no010/ESProbe/fw/components/DAP/source/spi_switch.c

/**
 * @file spi_switch.c
 * @author windowsair
 * @brief Switching between SPI mode and IO mode
 * @change: 2020-11-25 first version
 *          2021-2-11 Transmission mode switching test passed
 *          2022-9-15 Support ESP32C3
 * @version 0.4
 * @date 2021-9-15
 *
 * @copyright MIT License
 *
 */
#include "sdkconfig.h"

#include <stdbool.h>

#include "components/DAP/include/cmsis_compiler.h"
#include "components/DAP/include/spi_switch.h"
#include "components/DAP/include/gpio_common.h"

#ifdef CONFIG_IDF_TARGET_ESP32C3
#include "hal/cpu_ll.h"
#endif

#ifdef CONFIG_IDF_TARGET_ESP8266
    #define DAP_SPI SPI1
#elif defined CONFIG_IDF_TARGET_ESP32
    #define DAP_SPI SPI2
    // Note that the index starts at 0, so we are using function 2(SPI).
    #define FUNC_SPI 1
    #define SPI2_HOST 1
    #define SPI_LL_RST_MASK (SPI_OUT_RST | SPI_IN_RST | SPI_AHBM_RST | SPI_AHBM_FIFO_RST)
#elif defined CONFIG_IDF_TARGET_ESP32C3
    #define DAP_SPI GPSPI2
#elif defined CONFIG_IDF_TARGET_ESP32S3
    #define DAP_SPI GPSPI2
#else
    #error unknown hardware
#endif



#define ENTER_CRITICAL() portENTER_CRITICAL()
#define EXIT_CRITICAL() portEXIT_CRITICAL()

typedef enum {
    SPI_40MHz_DIV = 2,
    // SPI_80MHz_DIV = 1, //// FIXME: high speed clock
} spi_clk_div_t;



#ifdef CONFIG_IDF_TARGET_ESP8266
/**
 * @brief Initialize on first use
 *
 */
void DAP_SPI_Init()
{
    // The driving of GPIO should be stopped,
    // otherwise SPI has potential timing issues (This issue has been identified in OpenOCD)
    GPIO.out_w1tc = (0x1 << 13);
    GPIO.out_w1tc = (0x1 << 14);

    // Disable flash operation mode
    DAP_SPI.user.flash_mode = false;

    // Set to Master mode
    DAP_SPI.pin.slave_mode = false;
    DAP_SPI.slave.slave_mode = false;

    // Master uses the entire hardware buffer to improve transmission speed
    // If the following fields are enabled, only a part of the buffer is used
    DAP_SPI.user.usr_mosi_highpart = false;
    DAP_SPI.user.usr_miso_highpart = false;

    // Disable cs pin
    DAP_SPI.user.cs_setup = false;
    DAP_SPI.user.cs_hold = false;

    // Duplex transmit
    DAP_SPI.user.duplex = true;

    // SCLK delay setting
    DAP_SPI.user.ck_i_edge = true;
    DAP_SPI.ctrl2.mosi_delay_num = 0;
    DAP_SPI.ctrl2.miso_delay_num = 0;

    // DIO & QIO SPI disable
    DAP_SPI.user.fwrite_dual = false;
    DAP_SPI.user.fwrite_quad = false;
    DAP_SPI.user.fwrite_dio  = false;
    DAP_SPI.user.fwrite_qio  = false;
    DAP_SPI.ctrl.fread_dual  = false;
    DAP_SPI.ctrl.fread_quad  = false;
    DAP_SPI.ctrl.fread_dio   = false;
    DAP_SPI.ctrl.fread_qio   = false;
    DAP_SPI.ctrl.fastrd_mode = true;

    // Enable soft reset
    DAP_SPI.slave.sync_reset = true;

    // Set the clock polarity and phase CPOL = 1, CPHA = 0
    DAP_SPI.pin.ck_idle_edge = 1;  // HIGH while idle
    DAP_SPI.user.ck_out_edge = 0;


    // Set data bit order
    DAP_SPI.ctrl.wr_bit_order = 1; // SWD -> LSB
    DAP_SPI.ctrl.rd_bit_order = 1; // SWD -> LSB
    // Set data byte order
    DAP_SPI.user.wr_byte_order = 0;  // SWD -> litte_endian && Risc V -> litte_endian
    DAP_SPI.user.rd_byte_order = 0;  // SWD -> litte_endian && Risc V -> litte_endian

    // Set dummy
    DAP_SPI.user.usr_dummy = 0;

    // Initialize HSPI IO
    gpio_pin_reg_t pin_reg;

    PIN_FUNC_SELECT(PERIPHS_IO_MUX_MTMS_U, FUNC_HSPI_CLK); // GPIO14 is SPI CLK pin (Clock)
    GPIO.enable_w1ts |= (0x1 << 14); // PP Output
    pin_reg.val = READ_PERI_REG(GPIO_PIN_REG(14));
    pin_reg.pullup = 1;
    WRITE_PERI_REG(GPIO_PIN_REG(14), pin_reg.val);

    PIN_FUNC_SELECT(PERIPHS_IO_MUX_MTCK_U, FUNC_HSPID_MOSI); // GPIO13 is SPI MOSI pin (Master Data Out)
    GPIO.enable_w1ts |= (0x1 << 13);
    GPIO.pin[13].driver = 0; // PP Output or OD output
    pin_reg.val = READ_PERI_REG(GPIO_PIN_REG(13));
    pin_reg.pullup = 0;
    WRITE_PERI_REG(GPIO_PIN_REG(13), pin_reg.val);

#if (USE_SPI_SIO != 1)
    PIN_FUNC_SELECT(PERIPHS_IO_MUX_MTDI_U, FUNC_HSPIQ_MISO); // GPIO12 is SPI MISO pin (Master Data In)
    // esp8266 in is always connected
    pin_reg.val = READ_PERI_REG(GPIO_PIN_REG(12));
    pin_reg.pullup = 0;
    WRITE_PERI_REG(GPIO_PIN_REG(12), pin_reg.val);
#endif // (USE_SPI_SIO != 1)



    // Set spi clk div
    CLEAR_PERI_REG_MASK(PERIPHS_IO_MUX_CONF_U, SPI1_CLK_EQU_SYS_CLK);

    DAP_SPI.clock.clk_equ_sysclk = false;
    DAP_SPI.clock.clkdiv_pre = 0;
    DAP_SPI.clock.clkcnt_n = SPI_40MHz_DIV - 1;
    DAP_SPI.clock.clkcnt_h = SPI_40MHz_DIV / 2 - 1;
    DAP_SPI.clock.clkcnt_l = SPI_40MHz_DIV - 1;

    // Do not use command and addr
    DAP_SPI.user.usr_command = 0;
    DAP_SPI.user.usr_addr = 0;
}
#elif defined CONFIG_IDF_TARGET_ESP32
void DAP_SPI_Init()
{
    // In esp32, the driving of GPIO should be stopped,
    // otherwise there will be issue in the spi
    GPIO.out_w1tc = (0x1 << 13);
    GPIO.out_w1tc = (0x1 << 14);

    // Enable spi module, We use SPI2(HSPI)
    DPORT_SET_PERI_REG_MASK(DPORT_PERIP_CLK_EN_REG, DPORT_SPI2_CLK_EN);
    DPORT_CLEAR_PERI_REG_MASK(DPORT_PERIP_RST_EN_REG, DPORT_SPI2_RST);


    // We will use IO_MUX to get the maximum speed.
    GPIO.func_in_sel_cfg[HSPID_IN_IDX].sig_in_sel = 0;   // IO_MUX direct connnect
    PIN_INPUT_ENABLE(IO_MUX_GPIO13_REG);                 // MOSI
    GPIO.func_out_sel_cfg[13].oen_sel = 0;               // use output enable signal from peripheral
    GPIO.func_out_sel_cfg[13].oen_inv_sel = 0;           // do not invert the output value
    PIN_FUNC_SELECT(IO_MUX_GPIO13_REG, FUNC_SPI);

    // GPIO.func_in_sel_cfg[HSPIQ_IN_IDX].sig_in_sel = 0;
    // PIN_INPUT_ENABLE(IO_MUX_GPIO12_REG);                 // MISO
    // GPIO.func_out_sel_cfg[12].oen_sel = 0;
    // GPIO.func_out_sel_cfg[12].oen_inv_sel = 0;
    // PIN_FUNC_SELECT(IO_MUX_GPIO12_REG, FUNC_SPI);

    GPIO.func_in_sel_cfg[HSPICLK_IN_IDX].sig_in_sel = 0;
    PIN_INPUT_ENABLE(IO_MUX_GPIO14_REG);                 // SCLK
    GPIO.func_out_sel_cfg[14].oen_sel = 0;
    GPIO.func_out_sel_cfg[14].oen_inv_sel = 0;
    PIN_FUNC_SELECT(IO_MUX_GPIO14_REG, FUNC_SPI);


    // Not using DMA
    // esp32 only
    DPORT_SET_PERI_REG_BITS(DPORT_SPI_DMA_CHAN_SEL_REG, 3, 0, (SPI2_HOST * 2));


    // Reset DMA
    DAP_SPI.dma_conf.val |= SPI_LL_RST_MASK;
    DAP_SPI.dma_out_link.start = 0;
    DAP_SPI.dma_in_link.start = 0;
    DAP_SPI.dma_conf.val &= ~SPI_LL_RST_MASK;
    // Disable DMA
    DAP_SPI.dma_conf.dma_continue = 0;


    // Set to Master mode
    DAP_SPI.slave.slave_mode = false;


    // use all 64 bytes of the buffer
    DAP_SPI.user.usr_mosi_highpart = false;
    DAP_SPI.user.usr_miso_highpart = false;


    // Disable cs pin
    DAP_SPI.user.cs_setup = false;
    DAP_SPI.user.cs_hold = false;

    // Disable CS signal
    DAP_SPI.pin.cs0_dis = 1;
    DAP_SPI.pin.cs1_dis = 1;
    DAP_SPI.pin.cs2_dis = 1;

    // Duplex transmit
    DAP_SPI.user.doutdin = false;  // half dulex


    // Set data bit order
    DAP_SPI.ctrl.wr_bit_order = 1;   // SWD -> LSB
    DAP_SPI.ctrl.rd_bit_order = 1;   // SWD -> LSB
    // Set data byte order
    DAP_SPI.user.wr_byte_order = 0;  // SWD -> litte_endian && Risc V -> litte_endian
    DAP_SPI.user.rd_byte_order = 0;  // SWD -> litte_endian && Risc V -> litte_endian

    // Set dummy
    DAP_SPI.user.usr_dummy = 0; // not use

    // Set spi clk: 40Mhz 50% duty
    // CLEAR_PERI_REG_MASK(PERIPHS_IO_MUX_CONF_U, SPI1_CLK_EQU_SYS_CLK);

    // See esp32 TRM `SPI_CLOCK_REG`
    DAP_SPI.clock.clk_equ_sysclk = false;
    DAP_SPI.clock.clkdiv_pre = 0;
    DAP_SPI.clock.clkcnt_n = SPI_40MHz_DIV - 1;
    DAP_SPI.clock.clkcnt_h = SPI_40MHz_DIV / 2 - 1;
    DAP_SPI.clock.clkcnt_l = SPI_40MHz_DIV - 1;
    // Dummy is not required, but it may still need to be delayed
    // by half a clock cycle (espressif)


    // MISO delay setting
    DAP_SPI.user.ck_i_edge = true; //// TODO: may be used in slave mode?
    DAP_SPI.ctrl2.miso_delay_mode = 0;
    DAP_SPI.ctrl2.miso_delay_num = 0;


    // Set the clock polarity and phase CPOL = 1, CPHA = 0
    DAP_SPI.pin.ck_idle_edge = 1;  // HIGH while idle
    DAP_SPI.user.ck_out_edge = 0;

    // No command and addr for now
    DAP_SPI.user.usr_command = 0;
    DAP_SPI.user.usr_addr = 0;
}
#elif defined CONFIG_IDF_TARGET_ESP32C3
void DAP_SPI_Init()
{
    periph_ll_enable_clk_clear_rst(PERIPH_SPI2_MODULE);

    // In esp32, the driving of GPIO should be stopped,
    // otherwise there will be issue in the spi
    gpio_ll_set_level(&GPIO, GPIO_NUM_6, 0);
    gpio_ll_set_level(&GPIO, GPIO_NUM_7, 0);


    // We will use IO_MUX to get the maximum speed.
    GPIO.func_in_sel_cfg[FSPID_IN_IDX].sig_in_sel = 0;   // IO_MUX direct connnect
    PIN_INPUT_ENABLE(IO_MUX_GPIO7_REG);                  // MOSI
    GPIO.func_out_sel_cfg[7].oen_sel = 0;               // use output enable signal from peripheral
    GPIO.func_out_sel_cfg[7].oen_inv_sel = 0;           // do not invert the output value
    PIN_FUNC_SELECT(IO_MUX_GPIO7_REG, FUNC_MTDO_FSPID);


    GPIO.func_in_sel_cfg[FSPICLK_IN_IDX].sig_in_sel = 0;
    PIN_INPUT_ENABLE(IO_MUX_GPIO6_REG);                 // SCLK
    GPIO.func_out_sel_cfg[6].oen_sel = 0;
    GPIO.func_out_sel_cfg[6].oen_inv_sel = 0;
    PIN_FUNC_SELECT(IO_MUX_GPIO6_REG, FUNC_MTCK_FSPICLK);


    // Not using DMA
    // esp32c3 only
    DAP_SPI.user.usr_conf_nxt = 0;
    DAP_SPI.slave.usr_conf = 0;
    DAP_SPI.dma_conf.dma_rx_ena = 0;
    DAP_SPI.dma_conf.dma_tx_ena = 0;

    // Set to Master mode
    DAP_SPI.slave.slave_mode = false;

    // use all 64 bytes of the buffer
    DAP_SPI.user.usr_mosi_highpart = false;
    DAP_SPI.user.usr_miso_highpart = false;

    // Disable cs pin
    DAP_SPI.user.cs_setup = false;
    DAP_SPI.user.cs_hold = false;

    // Disable CS signal
    DAP_SPI.misc.cs0_dis = 1;
    DAP_SPI.misc.cs1_dis = 1;
    DAP_SPI.misc.cs2_dis = 1;
    DAP_SPI.misc.cs3_dis = 1;
    DAP_SPI.misc.cs4_dis = 1;
    DAP_SPI.misc.cs5_dis = 1;

    // Duplex transmit
    DAP_SPI.user.doutdin = false;  // half dulex

    // Set data bit order
    DAP_SPI.ctrl.wr_bit_order = 1;   // SWD -> LSB
    DAP_SPI.ctrl.rd_bit_order = 1;   // SWD -> LSB

    // Set dummy
    DAP_SPI.user.usr_dummy = 0; // not use

    // Set spi clk: 40Mhz 50% duty
    // CLEAR_PERI_REG_MASK(PERIPHS_IO_MUX_CONF_U, SPI1_CLK_EQU_SYS_CLK);

    // See esp32c3 TRM `SPI_CLOCK_REG`
    DAP_SPI.clock.clk_equ_sysclk = false;
    DAP_SPI.clock.clkdiv_pre = 0;
    DAP_SPI.clock.clkcnt_n = SPI_40MHz_DIV - 1;
    DAP_SPI.clock.clkcnt_h = SPI_40MHz_DIV / 2 - 1;
    DAP_SPI.clock.clkcnt_l = SPI_40MHz_DIV - 1;

    // MISO delay setting
    DAP_SPI.user.rsck_i_edge = true;
    DAP_SPI.din_mode.din0_mode = 0;
    DAP_SPI.din_mode.din1_mode = 0;
    DAP_SPI.din_mode.din2_mode = 0;
    DAP_SPI.din_mode.din3_mode = 0;
    DAP_SPI.din_num.din0_num = 0;
    DAP_SPI.din_num.din1_num = 0;
    DAP_SPI.din_num.din2_num = 0;
    DAP_SPI.din_num.din3_num = 0;

    // Set the clock polarity and phase CPOL = 1, CPHA = 0
    DAP_SPI.misc.ck_idle_edge = 1;  // HIGH while idle
    DAP_SPI.user.ck_out_edge = 0;

    // enable spi clock
    DAP_SPI.clk_gate.clk_en = 1;
    DAP_SPI.clk_gate.mst_clk_active = 1;
    DAP_SPI.clk_gate.mst_clk_sel = 1;

    // No command and addr for now
    DAP_SPI.user.usr_command = 0;
    DAP_SPI.user.usr_addr = 0;
}
#elif defined CONFIG_IDF_TARGET_ESP32S3
void DAP_SPI_Init()
{
    periph_ll_enable_clk_clear_rst(PERIPH_SPI2_MODULE);

    // In esp32, the driving of GPIO should be stopped,
    // otherwise there will be issue in the spi
    gpio_ll_set_level(&GPIO, GPIO_NUM_12, 0);
    gpio_ll_set_level(&GPIO, GPIO_NUM_11, 0);

    // We will use IO_MUX to get the maximum speed.
    gpio_ll_iomux_in(&GPIO, GPIO_NUM_12,FSPICLK_IN_IDX);
    gpio_ll_iomux_out(&GPIO, GPIO_NUM_12, FUNC_GPIO12_FSPICLK, 0);

    gpio_ll_iomux_in(&GPIO, GPIO_NUM_11,FSPID_IN_IDX);
    gpio_ll_iomux_out(&GPIO, GPIO_NUM_11, FUNC_GPIO11_FSPID, 0);

    GPIO.func_out_sel_cfg[GPIO_NUM_11].oen_sel = 0;
    GPIO.func_out_sel_cfg[GPIO_NUM_12].oen_sel = 0;

    // Not using DMA
    DAP_SPI.user.usr_conf_nxt = 0;
    DAP_SPI.slave.usr_conf = 0;
    DAP_SPI.dma_conf.dma_rx_ena = 0;
    DAP_SPI.dma_conf.dma_tx_ena = 0;

    // Set to Master mode
    DAP_SPI.slave.slave_mode = false;

    // use all 64 bytes of the buffer
    DAP_SPI.user.usr_mosi_highpart = false;
    DAP_SPI.user.usr_miso_highpart = false;

    // Disable cs pin
    DAP_SPI.user.cs_setup = false;
    DAP_SPI.user.cs_hold = false;

    // Disable CS signal
    DAP_SPI.misc.cs0_dis = 1;
    DAP_SPI.misc.cs1_dis = 1;
    DAP_SPI.misc.cs2_dis = 1;
    DAP_SPI.misc.cs3_dis = 1;
    DAP_SPI.misc.cs4_dis = 1;
    DAP_SPI.misc.cs5_dis = 1;

    // Duplex transmit
    DAP_SPI.user.doutdin = false;  // half dulex

    // Set data bit order
    DAP_SPI.ctrl.wr_bit_order = 1;   // SWD -> LSB
    DAP_SPI.ctrl.rd_bit_order = 1;   // SWD -> LSB

    // Set dummy
    DAP_SPI.user.usr_dummy = 0; // not use

    // Set spi clk: 40Mhz 50% duty
    // CLEAR_PERI_REG_MASK(PERIPHS_IO_MUX_CONF_U, SPI1_CLK_EQU_SYS_CLK);

    // See TRM `SPI_CLOCK_REG`
    DAP_SPI.clock.clk_equ_sysclk = false;
    DAP_SPI.clock.clkdiv_pre = 0;
    DAP_SPI.clock.clkcnt_n = SPI_40MHz_DIV - 1;
    DAP_SPI.clock.clkcnt_h = SPI_40MHz_DIV / 2 - 1;
    DAP_SPI.clock.clkcnt_l = SPI_40MHz_DIV - 1;

    // MISO delay setting
    DAP_SPI.user.rsck_i_edge = true;
    DAP_SPI.din_mode.din0_mode = 0;
    DAP_SPI.din_mode.din1_mode = 0;
    DAP_SPI.din_mode.din2_mode = 0;
    DAP_SPI.din_mode.din3_mode = 0;
    DAP_SPI.din_num.din0_num = 0;
    DAP_SPI.din_num.din1_num = 0;
    DAP_SPI.din_num.din2_num = 0;
    DAP_SPI.din_num.din3_num = 0;

    // Set the clock polarity and phase CPOL = 1, CPHA = 0
    DAP_SPI.misc.ck_idle_edge = 1;  // HIGH while idle
    DAP_SPI.user.ck_out_edge = 0;

    // enable spi clock
    DAP_SPI.clk_gate.clk_en = 1;
    DAP_SPI.clk_gate.mst_clk_active = 1;
    DAP_SPI.clk_gate.mst_clk_sel = 1;

    // No command and addr for now
    DAP_SPI.user.usr_command = 0;
    DAP_SPI.user.usr_addr = 0;
}
#endif


#ifdef CONFIG_IDF_TARGET_ESP8266
/**
 * @brief Switch to GPIO
 * Note: You may be able to pull the pin high in SPI mode, though you cannot set it to LOW
 */
__FORCEINLINE void DAP_SPI_Deinit()
{
    PIN_FUNC_SELECT(PERIPHS_IO_MUX_MTMS_U, FUNC_GPIO14);
    PIN_FUNC_SELECT(PERIPHS_IO_MUX_MTCK_U, FUNC_GPIO13); // MOSI
    // enable SWCLK output
    GPIO.enable_w1ts = 0x01 << 14;

    // enable MOSI output & input
    GPIO.enable_w1ts = 0x1 << 13;
}
#elif defined CONFIG_IDF_TARGET_ESP32
__FORCEINLINE void DAP_SPI_Deinit()
{
    PIN_FUNC_SELECT(GPIO_PIN_MUX_REG[14], PIN_FUNC_GPIO);
    PIN_FUNC_SELECT(GPIO_PIN_MUX_REG[13], PIN_FUNC_GPIO); // MOSI

    // enable SWCLK output
    GPIO.enable_w1ts = 0x01 << 14;

    // enable MOSI output & input
    GPIO.enable_w1ts = 0x1 << 13;
    PIN_INPUT_ENABLE(GPIO_PIN_MUX_REG[13]);
}
#elif defined CONFIG_IDF_TARGET_ESP32C3
__FORCEINLINE void DAP_SPI_Deinit()
{
    PIN_FUNC_SELECT(GPIO_PIN_MUX_REG[6], PIN_FUNC_GPIO);
    PIN_FUNC_SELECT(GPIO_PIN_MUX_REG[7], PIN_FUNC_GPIO); // MOSI

    // Route GPIO output to software-controlled GPIO_OUT_REG (SIG_GPIO_OUT_IDX=256)
    // instead of dedic_gpio (CPU_GPIO_OUTx_IDX), since dedic_gpio CSR instructions
    // are not available in ESP-IDF 5.5 and gpio_ll_set_level() writes GPIO_OUT_REG.
    GPIO.func_out_sel_cfg[GPIO_NUM_6].out_sel = SIG_GPIO_OUT_IDX;
    GPIO.func_out_sel_cfg[GPIO_NUM_6].oen_sel = 0;

    GPIO.func_out_sel_cfg[GPIO_NUM_7].out_sel = SIG_GPIO_OUT_IDX;
    GPIO.func_out_sel_cfg[GPIO_NUM_7].oen_sel = 0;

    GPIO.func_in_sel_cfg[FSPID_IN_IDX].sig_in_sel = 0;
    GPIO.func_in_sel_cfg[FSPID_IN_IDX].in_sel = GPIO_NUM_7;

    // enable SWCLK/MOSI output
    gpio_ll_output_enable(&GPIO, GPIO_NUM_6);
    gpio_ll_output_enable(&GPIO, GPIO_NUM_7);
    PIN_INPUT_ENABLE(GPIO_PIN_MUX_REG[7]);
}
#elif defined CONFIG_IDF_TARGET_ESP32S3
__FORCEINLINE void DAP_SPI_Deinit()
{
    gpio_ll_iomux_func_sel(GPIO_PIN_MUX_REG[GPIO_NUM_12], PIN_FUNC_GPIO);
    gpio_ll_iomux_func_sel(GPIO_PIN_MUX_REG[GPIO_NUM_11], PIN_FUNC_GPIO); // MOSI

    // SWCLK output
    GPIO.func_out_sel_cfg[GPIO_NUM_12].func_sel = CORE1_GPIO_OUT1_IDX;
    GPIO.func_out_sel_cfg[GPIO_NUM_12].oen_sel = 1;
    gpio_ll_output_enable(&GPIO, GPIO_NUM_12);

    // SWDIO outout
    GPIO.func_out_sel_cfg[GPIO_NUM_11].func_sel = CORE1_GPIO_OUT0_IDX;
    GPIO.func_out_sel_cfg[GPIO_NUM_11].oen_sel = 1;
    gpio_ll_output_enable(&GPIO, GPIO_NUM_11);

    // SWDIO input
    GPIO.func_in_sel_cfg[CORE1_GPIO_IN0_IDX].sig_in_sel = 1;
    GPIO.func_in_sel_cfg[CORE1_GPIO_IN0_IDX].func_sel = GPIO_NUM_11;
    gpio_ll_input_enable(&GPIO, GPIO_NUM_11);
}
#endif


#ifdef CONFIG_IDF_TARGET_ESP32
/**
 * @brief Gain control of SPI
 *
 */
__FORCEINLINE void DAP_SPI_Acquire()
{
    PIN_FUNC_SELECT(IO_MUX_GPIO14_REG, FUNC_SPI);
}


/**
 * @brief Release control of SPI
 *
 */
__FORCEINLINE void DAP_SPI_Release()
{
    PIN_FUNC_SELECT(GPIO_PIN_MUX_REG[14], PIN_FUNC_GPIO);
    GPIO.enable_w1ts = (0x01 << 14);
}
#elif defined CONFIG_IDF_TARGET_ESP32C3
__FORCEINLINE void DAP_SPI_Acquire()
{
    PIN_FUNC_SELECT(IO_MUX_GPIO6_REG, FUNC_MTCK_FSPICLK);
}

__FORCEINLINE void DAP_SPI_Release()
{
    PIN_FUNC_SELECT(IO_MUX_GPIO6_REG, FUNC_MTCK_GPIO6);
}
#elif defined CONFIG_IDF_TARGET_ESP32S3
/**
 * @brief Gain control of SPI
 *
 */
__FORCEINLINE void DAP_SPI_Acquire()
{
    gpio_ll_iomux_func_sel(GPIO_PIN_MUX_REG[GPIO_NUM_12], FUNC_GPIO12_FSPICLK);
}


/**
 * @brief Release control of SPI
 *
 */
__FORCEINLINE void DAP_SPI_Release()
{
    gpio_ll_iomux_func_sel(GPIO_PIN_MUX_REG[GPIO_NUM_12], FUNC_GPIO12_GPIO12);
}
#endif
