no010/ESProbe/fw/main/usbip_server.c

#include <stdint.h>
#include <string.h>

#include "main/usbip_server.h"
#include "main/DAP_handle.h"
#include "main/wifi_configuration.h"

#include "components/USBIP/usb_handle.h"
#include "components/USBIP/usb_descriptor.h"

#include "lwip/err.h"
#include "lwip/sockets.h"
#include "lwip/sys.h"
#include <lwip/netdb.h>

#ifndef likely
#define likely(x)      __builtin_expect(!!(x), 1)
#endif

#ifndef unlikely
#define unlikely(x)    __builtin_expect(!!(x), 0)
#endif

// Set to 1 to enable verbose hex-dump logging (slows down USB enumeration)
#define USBIP_DEBUG_VERBOSE 0

// attach helper function
static int read_stage1_command(uint8_t *buffer, uint32_t length);
static void handle_device_list(uint8_t *buffer, uint32_t length);
static void handle_device_attach(uint8_t *buffer, uint32_t length);
static void send_stage1_header(uint16_t command, uint32_t status);
static void send_device_list();
static void send_device_info();
static void send_interface_info();

// emulate helper function
static void pack(void *data, int size);
static void unpack(void *data, int size);

static void handle_unlink(usbip_stage2_header *header);
// unlink helper function
static void send_stage2_unlink(usbip_stage2_header *req_header);


#if (USBIP_DEBUG_VERBOSE == 1)
static void debug_dump_bytes(const char *tag, const uint8_t *data, size_t length)
{
    char line[128];
    size_t offset = 0;

    while (offset < length) {
        size_t chunk = ((length - offset) > 16U) ? 16U : (length - offset);
        int pos = snprintf(line, sizeof(line), "%s +%02u:", tag, (unsigned)offset);
        for (size_t i = 0; i < chunk && pos > 0 && pos < (int)sizeof(line); ++i) {
            pos += snprintf(&line[pos], sizeof(line) - (size_t)pos, " %02X", data[offset + i]);
        }
        os_printf("%s\r\n", line);
        offset += chunk;
    }
}

static void debug_dump_usbip_header(const char *tag, const usbip_stage2_header *header)
{
    debug_dump_bytes(tag, (const uint8_t *)header, sizeof(usbip_stage2_header));
}
#else
#define debug_dump_bytes(tag, data, length)     ((void)0)
#define debug_dump_usbip_header(tag, header)    ((void)0)
#endif

int usbip_network_send(int s, const void *dataptr, size_t size, int flags) {
#if (USE_KCP == 1)
    return kcp_network_send(dataptr, size);
#elif (USE_TCP_NETCONN == 1)
    return tcp_netconn_send(dataptr, size);
#else // BSD style
    const uint8_t *data = (const uint8_t *)dataptr;
    size_t remaining = size;

    while (remaining > 0) {
        int sent = send(s, data, remaining, flags);
        if (sent <= 0) {
            return sent;
        }
        data += sent;
        remaining -= (size_t)sent;
    }

    return (int)size;
#endif
}

static int attach(uint8_t *buffer, uint32_t length)
{
    int command = read_stage1_command(buffer, length);
    if (command < 0)
    {
        return -1;
    }

    switch (command)
    {
    case USBIP_STAGE1_CMD_DEVICE_LIST: // OP_REQ_DEVLIST
        handle_device_list(buffer, length);
        break;

    case USBIP_STAGE1_CMD_DEVICE_ATTACH: // OP_REQ_IMPORT
        handle_device_attach(buffer, length);
        break;

    default:
        os_printf("attach Unknown command: %d\r\n", command);
        break;
    }
    return 0;
}

static int read_stage1_command(uint8_t *buffer, uint32_t length)
{
    if (length < sizeof(usbip_stage1_header))
    {
        return -1;
    }
    usbip_stage1_header *req = (usbip_stage1_header *)buffer;
    uint16_t cmd_raw = req->command;
    int cmd = (int)(ntohs(req->command) & 0xFF);
    os_printf("read_stage1_command: raw=0x%04X ret=0x%02X buf=%02X%02X%02X%02X%02X%02X%02X%02X\r\n",
              (unsigned)cmd_raw, (unsigned)cmd,
              buffer[0], buffer[1], buffer[2], buffer[3],
              buffer[4], buffer[5], buffer[6], buffer[7]);
    return cmd;
}

static void handle_device_list(uint8_t *buffer, uint32_t length)
{
    os_printf("Handling dev list request...\r\n");
    send_stage1_header(USBIP_STAGE1_CMD_DEVICE_LIST, 0);
    send_device_list();
}

static void handle_device_attach(uint8_t *buffer, uint32_t length)
{
    os_printf("Handling dev attach request...\r\n");

    //char bus[USBIP_BUSID_SIZE];
    if (length < sizeof(USBIP_BUSID_SIZE))
    {
        os_printf("handle device attach failed!\r\n");
        return;
    }
    //client.readBytes((uint8_t *)bus, USBIP_BUSID_SIZE);

    send_stage1_header(USBIP_STAGE1_CMD_DEVICE_ATTACH, 0);

    send_device_info();
}

static void send_stage1_header(uint16_t command, uint32_t status)
{
    os_printf("Sending header...\r\n");
    usbip_stage1_header header = {0};
    header.version = htons(273); ////TODO:  273???
    // may be : https://github.com/Oxalin/usbip_windows/issues/4

    header.command = htons(command);
    header.status = htonl(status);

    usbip_network_send(kSock, (uint8_t *)&header, sizeof(usbip_stage1_header), 0);
}

static void send_device_list()
{
    os_printf("Sending device list...\r\n");

    // send device list size:
    os_printf("Sending device list size...\r\n");
    usbip_stage1_response_devlist response_devlist = {0};

    // we have only 1 device, so:
    response_devlist.list_size = htonl(1);

    usbip_network_send(kSock, (uint8_t *)&response_devlist, sizeof(usbip_stage1_response_devlist), 0);

    // may be foreach:

    {
        // send device info:
        send_device_info();
        // send device interfaces: // (1)
        send_interface_info();
    }
}

static void send_device_info()
{
    os_printf("Sending device info...\r\n");
    usbip_stage1_usb_device device = {0};

    strcpy(device.path, "/sys/devices/pci0000:00/0000:00:01.2/usb1/1-1");
    strcpy(device.busid, "1-1");

    device.busnum = htonl(1);
    device.devnum = htonl(1);
    device.speed = htonl(2); // USB_SPEED_FULL (12 Mbps).  WiFi cannot sustain High Speed.

    device.idVendor = htons(USBD0_DEV_DESC_IDVENDOR);
    device.idProduct = htons(USBD0_DEV_DESC_IDPRODUCT);
    device.bcdDevice = htons(USBD0_DEV_DESC_BCDDEVICE);

    device.bDeviceClass = 0x00; // We need to use a device other than the USB-IF standard, set to 0x00
    device.bDeviceSubClass = 0x00;
    device.bDeviceProtocol = 0x00;

    device.bConfigurationValue = 1;
    device.bNumConfigurations = 1;
    device.bNumInterfaces = 1;

    usbip_network_send(kSock, (uint8_t *)&device, sizeof(usbip_stage1_usb_device), 0);
}

static void send_interface_info()
{
    os_printf("Sending interface info...\r\n");
    usbip_stage1_usb_interface interface = {0};
    interface.bInterfaceClass = USBD_CUSTOM_CLASS0_IF0_CLASS;
    interface.bInterfaceSubClass = USBD_CUSTOM_CLASS0_IF0_SUBCLASS;
    interface.bInterfaceProtocol = USBD_CUSTOM_CLASS0_IF0_PROTOCOL;
    interface.padding = 0; // shall be set to zero

    usbip_network_send(kSock, (uint8_t *)&interface, sizeof(usbip_stage1_usb_interface), 0);
}

static int usbip_urb_process(uint8_t *base, uint32_t length)
{
    usbip_stage2_header *header = (usbip_stage2_header *)base;
    uint8_t *data;
    uint32_t command, dir, ep;
    uint32_t unlink_count = 0;
    bool may_has_data;
    int sz, ret;
    int dap_req_num = 0;
    uint32_t ep_data_length = 0;

    while (1) {
        // header
        data = base;
        sz = 48; // for USBIP_CMD_SUBMIT/USBIP_CMD_UNLINK
        do {
            ret = recv(kSock, data, sz, 0);
            if (ret <= 0)
                goto out;
            sz -= ret;
            data += ret;
        } while (sz > 0);

        command = ntohl(header->base.command);
        dir = ntohl(header->base.direction);
        ep = ntohl(header->base.ep);
        may_has_data = (command == USBIP_STAGE2_REQ_SUBMIT && dir == USBIP_DIR_OUT);
        ep_data_length = may_has_data ? ntohl(header->u.cmd_submit.data_length) : 0;
        sz = (int)ep_data_length;

        while (sz) {
                ret = recv(kSock, data, sz, 0);
                if (ret <= 0)
                    goto out;
                sz -= ret;
                data += ret;
        }

        if (likely(command == USBIP_STAGE2_REQ_SUBMIT)) {
            if (likely(ep == 1 && dir == USBIP_DIR_IN)) {
                if (dap_req_num > 0) {
                    int fr = fast_reply(base, sizeof(usbip_stage2_header), dap_req_num);
                    if (fr) {
                        dap_req_num--;
                    } else {
                        save_in_header(header);
                    }
                } else {
                    // No OUT pending yet (flush read from start_rx() or race).
                    // Return an empty ACK immediately so the host does not
                    // timeout and UNLINK.  With the pyusb_v2_backend patch
                    // OUT now arrives before IN for real commands.
                    fast_reply(base, sizeof(usbip_stage2_header), 0);
                }
            } else if (likely(ep == 1 && dir == USBIP_DIR_OUT)) {
                dap_req_num++;
                handle_dap_data_request(header, ep_data_length);
            } else if (ep == 0) {
                unpack(base, sizeof(usbip_stage2_header));
#if (USBIP_DEBUG_VERBOSE == 1)
                os_printf("EP0_REQ seq=%lu dir=%lu ep=%lu len=%ld type=%02X req=%02X wValue=%02X%02X wIndex=%02X%02X wLength=%02X%02X\r\n",
                          (unsigned long)header->base.seqnum,
                          (unsigned long)header->base.direction,
                          (unsigned long)header->base.ep,
                          (long)header->u.cmd_submit.data_length,
                          header->u.cmd_submit.request.bmRequestType,
                          header->u.cmd_submit.request.bRequest,
                          header->u.cmd_submit.request.wValue.u8hi,
                          header->u.cmd_submit.request.wValue.u8lo,
                          header->u.cmd_submit.request.wIndex.u8hi,
                          header->u.cmd_submit.request.wIndex.u8lo,
                          header->u.cmd_submit.request.wLength.u8hi,
                          header->u.cmd_submit.request.wLength.u8lo);
                debug_dump_usbip_header("EP0_REQ_HDR", header);
#endif
                handleUSBControlRequest(header);
            } else {
                // ep3 reserved for SWO
                os_printf("ep reserved:%d\r\n", ep);
                send_stage2_submit(header, 0, 0);
            }
        } else if (command == USBIP_STAGE2_REQ_UNLINK) {
            if (unlink_count == 0 || unlink_count % 100 == 0)
                os_printf("unlink\r\n");
            unlink_count++;
            unpack(base, sizeof(usbip_stage2_header));
            handle_unlink(header);
        } else {
            os_printf("emulate unknown command:%d\r\n", command);
            return -1;
        }

        if (has_pending_in() && dap_req_num > 0) {
            usbip_stage2_header saved_header;
            if (peek_oldest_in_header(&saved_header)) {
                if (fast_reply((uint8_t *)&saved_header, sizeof(usbip_stage2_header), dap_req_num)) {
                    dap_req_num--;
                    get_oldest_in_header(&saved_header); // consume it
                }
            }
        }
    }

out:
    if (ret < 0)
        os_printf("recv failed: errno %d\r\n", errno);
    return ret;
}

int usbip_worker(uint8_t *base, uint32_t length, enum usbip_server_state_t *state)
{
    uint8_t *data;
    int pre_read_sz = 4;
    int sz, ret;

    os_printf("usbip_worker enter state=%d\r\n", (int)*state);

    // OP_REQ_DEVLIST status field
    if (*state == WAIT_DEVLIST) {
        data = base + 4;
        sz = 8 - pre_read_sz;
        do {
            ret = recv(kSock, data, sz, 0);
            if (ret <= 0)
                return ret;
            sz -= ret;
            data += ret;
        } while (sz > 0);

        os_printf("usbip_worker calling attach(base,8)\r\n");
        ret = attach(base, 8);
        if (ret)
            return ret;

        pre_read_sz = 0;
    }

    *state = WAIT_IMPORT;
    // OP_REQ_IMPORT
    data = base + pre_read_sz;
    sz = 40 - pre_read_sz;
    do {
        ret = recv(kSock, data, sz, 0);
        if (ret <= 0)
            return ret;
        sz -= ret;
        data += ret;
    } while (sz > 0);

    os_printf("usbip_worker calling attach(base,40)\r\n");
    ret = attach(base, 40);
    if (ret)
        return ret;

    // URB process
    *state = WAIT_URB;
    ret = usbip_urb_process(base, length);
    if (ret) {
        *state = WAIT_DEVLIST;
        return ret;
    }

    return 0;
}

/**
 * @brief Pack the following packets(Offset 0x00 - 0x28):
 *       - cmd_submit
 *       - ret_submit
 *       - cmd_unlink
 *       - ret_unlink
 *
 * @param data Point to packets header
 * @param size Packets header size
 */
static void pack(void *data, int size)
{

    // Ignore the setup field
    int sz = (size / sizeof(uint32_t)) - 2;
    uint32_t *ptr = (uint32_t *)data;

    for (int i = 0; i < sz; i++)
    {

        ptr[i] = htonl(ptr[i]);
    }
}

/**
 * @brief Unack the following packets(Offset 0x00 - 0x28):
 *       - cmd_submit
 *       - ret_submit
 *       - cmd_unlink
 *       - ret_unlink
 *
 * @param data Point to packets header
 * @param size  packets header size
 */
static void unpack(void *data, int size)
{

    // Ignore the setup field
    int sz = (size / sizeof(uint32_t)) - 2;
    uint32_t *ptr = (uint32_t *)data;

    for (int i = 0; i < sz; i++)
    {
        ptr[i] = ntohl(ptr[i]);
    }
}

void send_stage2_submit(usbip_stage2_header *req_header, int32_t status, int32_t data_length)
{
    uint32_t request_devid = req_header->base.devid;
    uint32_t request_direction = req_header->base.direction;
    uint32_t request_ep = req_header->base.ep;

    req_header->base.command = USBIP_STAGE2_RSP_SUBMIT;
    req_header->base.devid = request_devid;
    req_header->base.direction = !request_direction;
    req_header->base.ep = request_ep;

    memset(&(req_header->u), 0, sizeof(req_header->u));

    req_header->u.ret_submit.status = status;
    req_header->u.ret_submit.data_length = data_length;
    req_header->u.ret_submit.number_of_packets = 0;
    // already unpacked
    pack(req_header, sizeof(usbip_stage2_header));

#if (USBIP_DEBUG_VERBOSE == 1)
    if (ntohl(req_header->base.seqnum) != 0) {
        os_printf("RET_SUBMIT seq=%lu status=%ld len=%ld\r\n",
                  (unsigned long)ntohl(req_header->base.seqnum),
                  (long)status,
                  (long)data_length);
        debug_dump_usbip_header("RET_SUBMIT_HDR", req_header);
    }
#endif

    usbip_network_send(kSock, req_header, sizeof(usbip_stage2_header), 0);
}

void send_stage2_submit_data(usbip_stage2_header *req_header, int32_t status, const void *const data, int32_t data_length)
{
    uint8_t send_buf[sizeof(usbip_stage2_header) + 512];
    size_t total_len = sizeof(usbip_stage2_header);

    // Setup header (same logic as send_stage2_submit)
    uint32_t request_devid = req_header->base.devid;
    uint32_t request_direction = req_header->base.direction;
    uint32_t request_ep = req_header->base.ep;

    req_header->base.command = USBIP_STAGE2_RSP_SUBMIT;
    req_header->base.devid = request_devid;
    req_header->base.direction = !request_direction;
    req_header->base.ep = request_ep;

    memset(&(req_header->u), 0, sizeof(req_header->u));

    req_header->u.ret_submit.status = status;
    req_header->u.ret_submit.data_length = data_length;
    req_header->u.ret_submit.number_of_packets = 0;

    pack(req_header, sizeof(usbip_stage2_header));

    // Copy header + data into single buffer to avoid split-send latency
    memcpy(send_buf, req_header, sizeof(usbip_stage2_header));
    if (data && data_length > 0) {
        int32_t copy_len = data_length;
        if (copy_len > 512) {
            os_printf("WARN: send_stage2_submit_data len=%d > 512, truncating!\r\n", copy_len);
            copy_len = 512;
        }
        memcpy(send_buf + sizeof(usbip_stage2_header), data, copy_len);
        total_len += copy_len;
    }

    usbip_network_send(kSock, send_buf, total_len, 0);
}

void send_stage2_submit_data_fast(usbip_stage2_header *req_header, const void *const data, int32_t data_length)
{
    uint8_t * send_buf = (uint8_t *)req_header;

    req_header->base.command = PP_HTONL(USBIP_STAGE2_RSP_SUBMIT);
    // On little-endian CPUs htonl(!x) with network-byte-order x happens to
    // produce the correct flipped network-byte-order value, which is what the
    // original upstream code relied on.  Preserve that behaviour.
    req_header->base.direction = htonl(!(req_header->base.direction));

    memset(&(req_header->u), 0, sizeof(req_header->u));
    req_header->u.ret_submit.status = PP_HTONL(0);
    req_header->u.ret_submit.data_length = htonl(data_length);
    req_header->u.ret_submit.number_of_packets = htonl(0);

    // payload
    if (data)
        memcpy(&send_buf[sizeof(usbip_stage2_header)], data, data_length);

#if (USBIP_DEBUG_VERBOSE == 1)
    if (ntohl(req_header->base.seqnum) != 0) {
        os_printf("RET_SUBMIT_FAST seq=%lu len=%ld\r\n",
                  (unsigned long)ntohl(req_header->base.seqnum),
                  (long)data_length);
        debug_dump_usbip_header("RET_FAST_HDR", req_header);
        if (data) {
            size_t dump_len = ((size_t)data_length > 32U) ? 32U : (size_t)data_length;
            debug_dump_bytes("RET_FAST_DATA", (const uint8_t *)data, dump_len);
        }
    }
#endif

    int sent = usbip_network_send(kSock, send_buf, sizeof(usbip_stage2_header) + data_length, 0);
    os_printf("fast_send ret=%d len=%d\r\n", sent, (int)(sizeof(usbip_stage2_header) + data_length));
}


static void handle_unlink(usbip_stage2_header *header)
{
    uint32_t unlink_seqnum = ntohl(header->u.cmd_unlink.seqnum);
    handle_dap_unlink(unlink_seqnum);
    send_stage2_unlink(header);
}

static void send_stage2_unlink(usbip_stage2_header *req_header)
{
    req_header->base.command = USBIP_STAGE2_RSP_UNLINK;
    // usbip-win2 expects direction = USBIP_DIR_OUT in RET_UNLINK, matching original upstream
    req_header->base.direction = USBIP_DIR_OUT;

    memset(&(req_header->u), 0, sizeof(req_header->u));

    // usbip-win2 treats any non-zero status as "unlink succeeded".
    // The precise value is -ECONNRESET, but -1 is sufficient and matches original code.
    req_header->u.ret_unlink.status = -1;

    pack(req_header, sizeof(usbip_stage2_header));

    os_printf("RET_UNLINK seq=%lu status=%ld\r\n",
              (unsigned long)ntohl(req_header->base.seqnum),
              (long)-1);
    debug_dump_usbip_header("RET_UNLINK_HDR", req_header);

    usbip_network_send(kSock, req_header, sizeof(usbip_stage2_header), 0);
}
